nuclearfurnace/smartstand/enclosure/component-library/C0805.SLDPRT

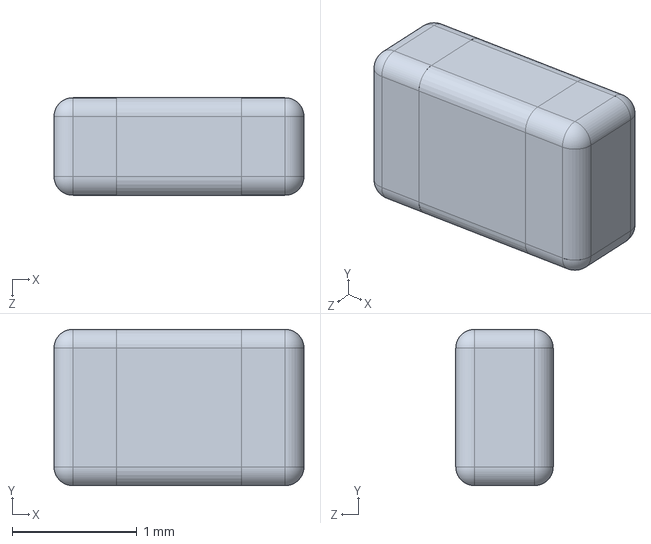
[picture p15: CAD file, 2017-02-09]
enclosure/component-library/C0805.SLDPRT
2.00 x 1.25 x 0.78 mm
