nuclearfurnace/smartstand/enclosure/component-library/R0402.SLDPRT

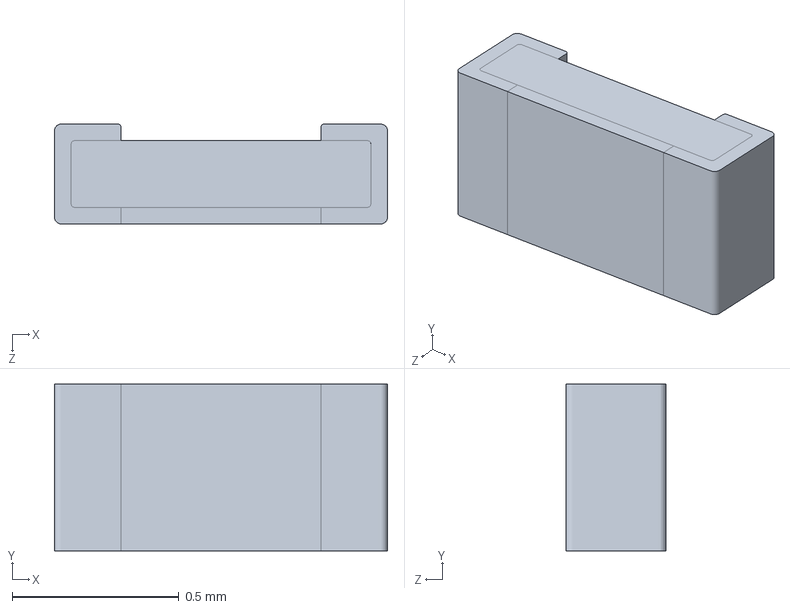
[picture p16: CAD file, 2017-02-09]
enclosure/component-library/R0402.SLDPRT
1.00 x 0.5 x 0.3 mm
