nuclearfurnace/smartstand/enclosure/component-library/RK14K1240A4S.SLDPRT

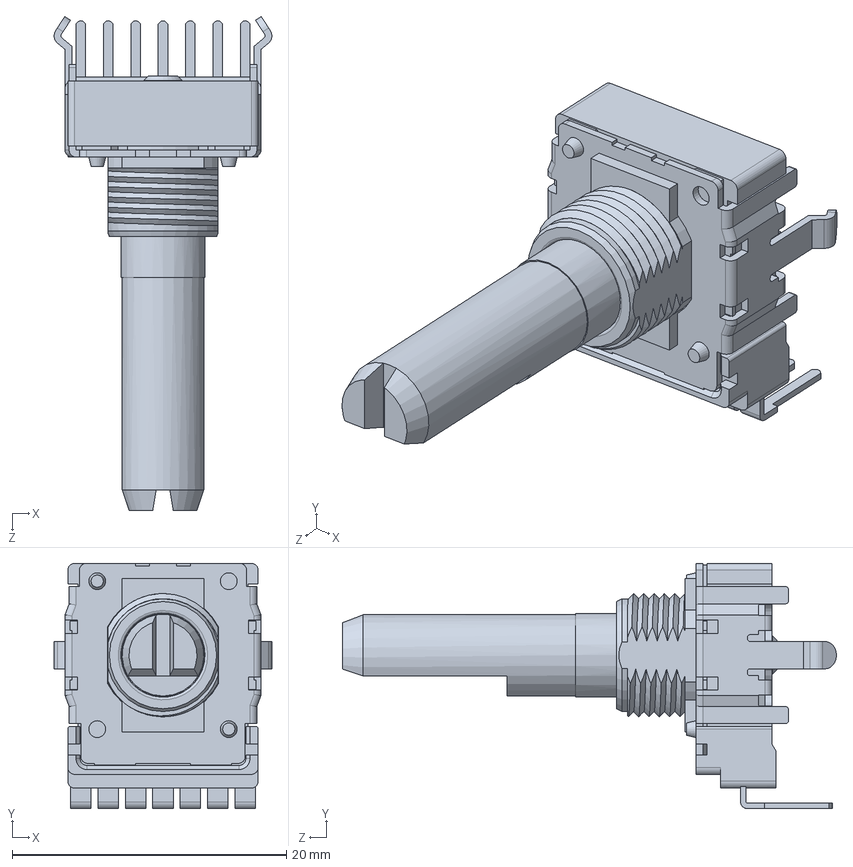
[picture p17: CAD file, 2017-02-09]
enclosure/component-library/RK14K1240A4S.SLDPRT
15.9 x 17.9 x 36.1 mm
