nuclearfurnace/smartstand/enclosure/smartstand-enclosure-base.SLDPRT

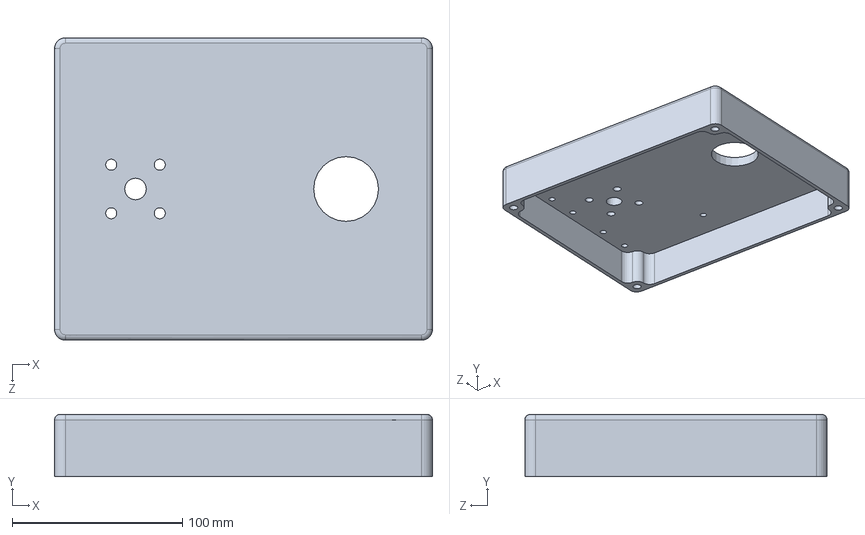
[picture p18: CAD file, 2018-03-22]
enclosure/smartstand-enclosure-base.SLDPRT
222.2 x 36.5 x 177.8 mm
