nuclearfurnace/smartstand/enclosure/component-library/R1206.SLDPRT

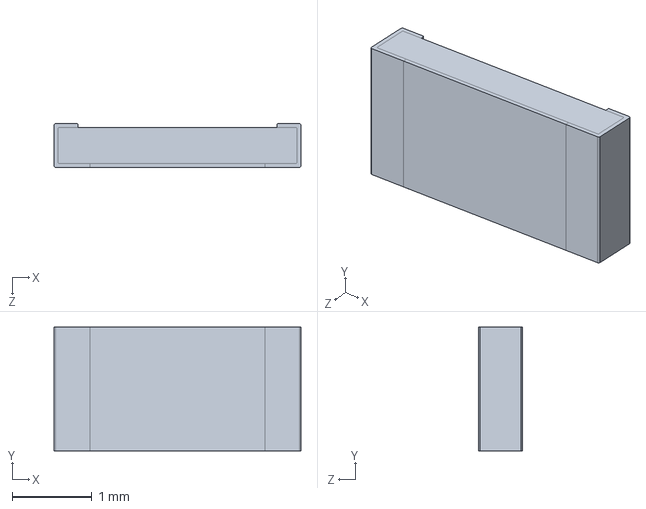
[picture p19: CAD file, 2017-02-09]
enclosure/component-library/R1206.SLDPRT
3.10 x 1.55 x 0.55 mm
