nuclearfurnace/smartstand/enclosure/smartstand-enclosure-sensor-cover.SLDPRT

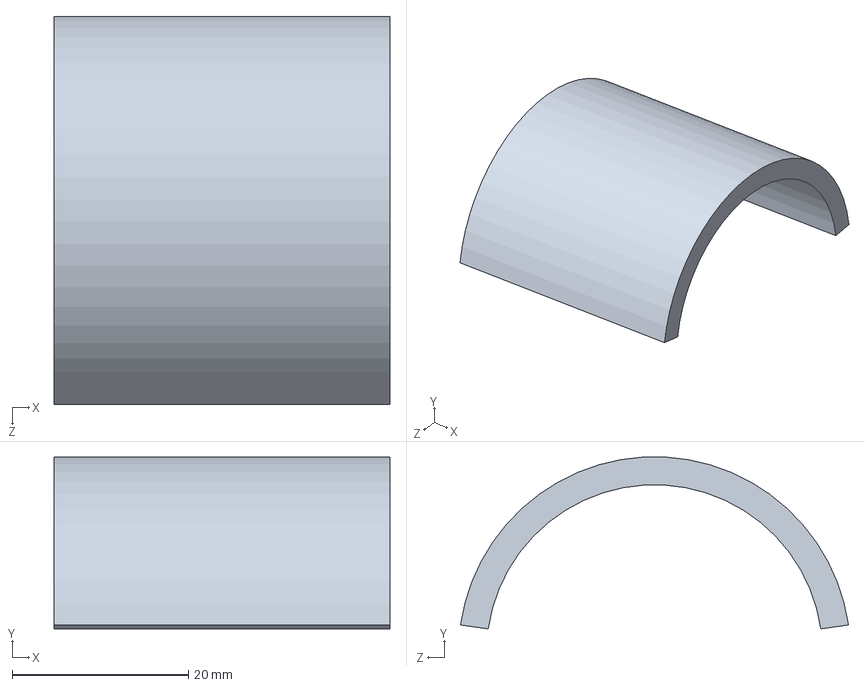
[picture p20: CAD file, 2018-03-22]
enclosure/smartstand-enclosure-sensor-cover.SLDPRT
38.1 x 19.5 x 44.0 mm
