nuclearfurnace/smartstand/enclosure/component-library/R0805.SLDPRT

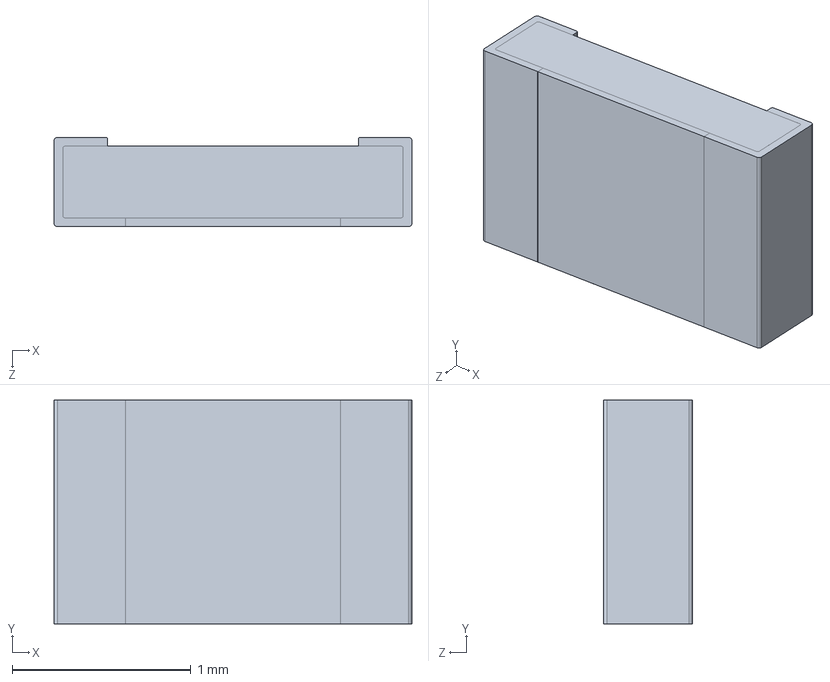
[picture p21: CAD file, 2017-02-09]
enclosure/component-library/R0805.SLDPRT
2.00 x 1.25 x 0.5 mm
