nuclearfurnace/smartstand/enclosure/component-library/R2010.SLDPRT

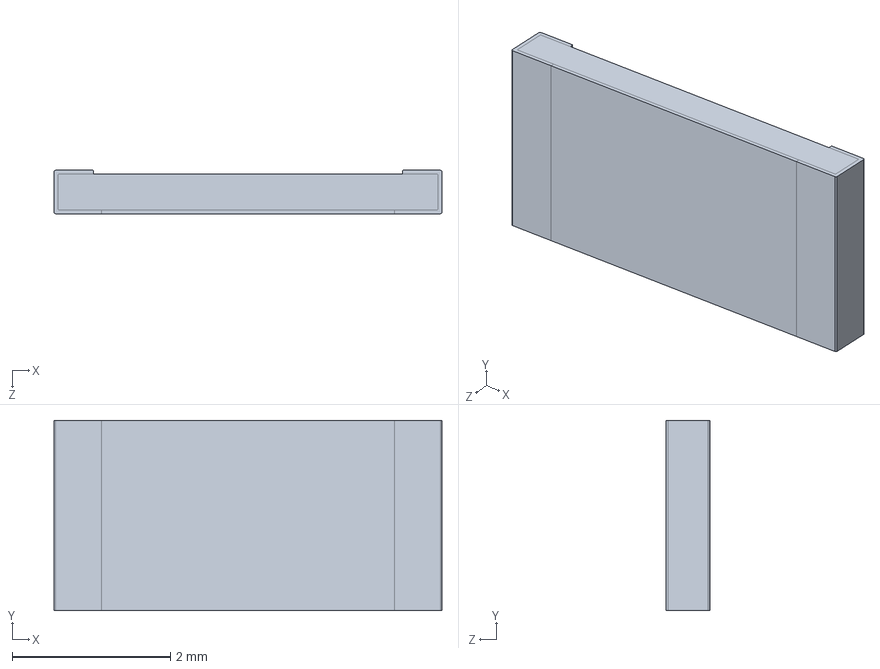
[picture p22: CAD file, 2017-02-09]
enclosure/component-library/R2010.SLDPRT
4.90 x 2.40 x 0.55 mm
