nuclearfurnace/smartstand/enclosure/smartstand-enclosure-upright.SLDPRT

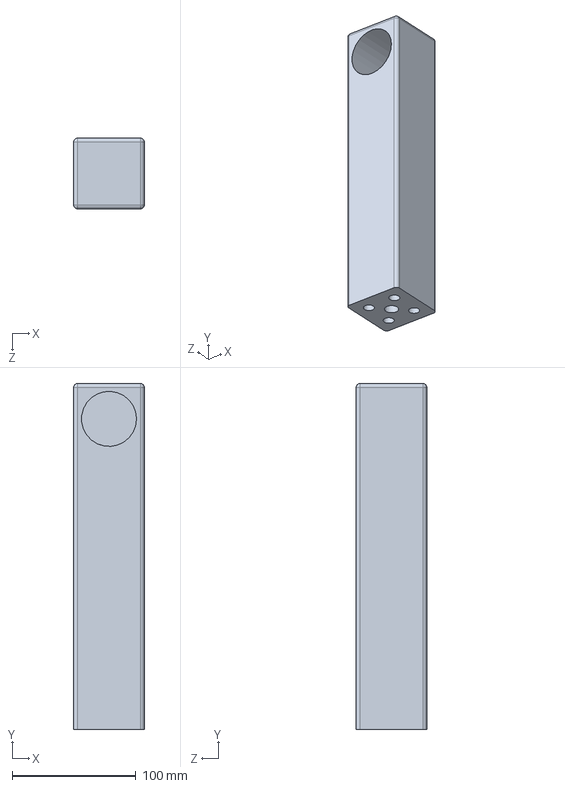
[picture p23: CAD file, 2018-03-22]
enclosure/smartstand-enclosure-upright.SLDPRT
57.2 x 279.4 x 57.1 mm
