nuclearfurnace/smartstand/enclosure/PJRAN2X1U01AUX.sldprt

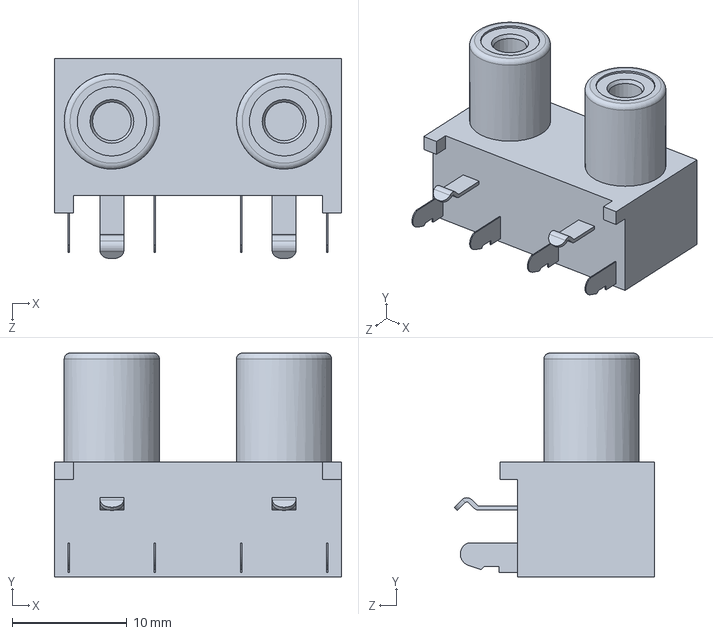
[picture p24: CAD file, 2018-03-22]
enclosure/PJRAN2X1U01AUX.sldprt
25.0 x 19.5 x 17.5 mm
